simojo/pit-viper-inspired-sensing/data/mechanical-data/Mechanical platform  & pictures/Final design.png

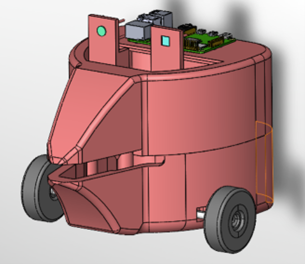
data/mechanical-data/Mechanical platform & pictures/Final design.png
