simojo/pit-viper-inspired-sensing/data/mechanical-data/Mechanical platform  & pictures/Concept generation - white board discusssion.png

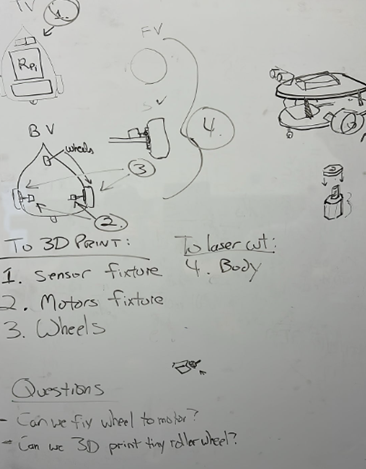
data/mechanical-data/Mechanical platform & pictures/Concept generation - white board discusssion.png
